jkrame1/Betweener/Hardware/panel/Kyle Werle Betweener and sidecar.jpg

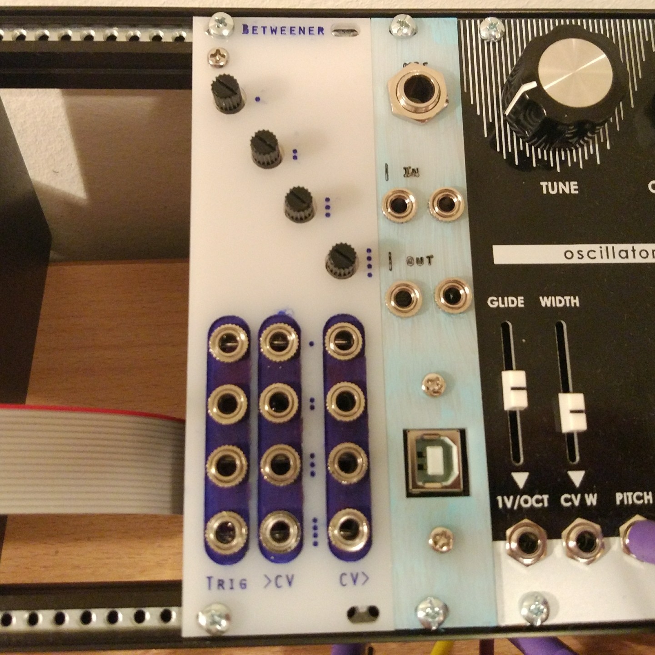
Hardware/panel/Kyle Werle Betweener and sidecar.jpg
