jkrame1/Betweener/Hardware/Betweener Build Images/Betweener-01.jpg

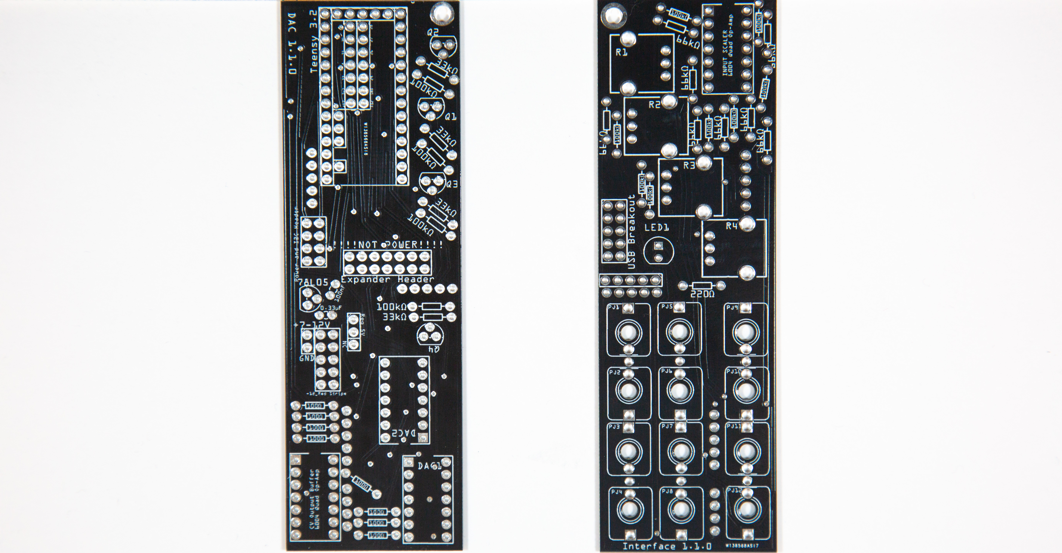
Hardware/Betweener Build Images/Betweener-01.jpg
