jkrame1/Betweener/Hardware/Betweener Build Images/Betweener-02.jpg

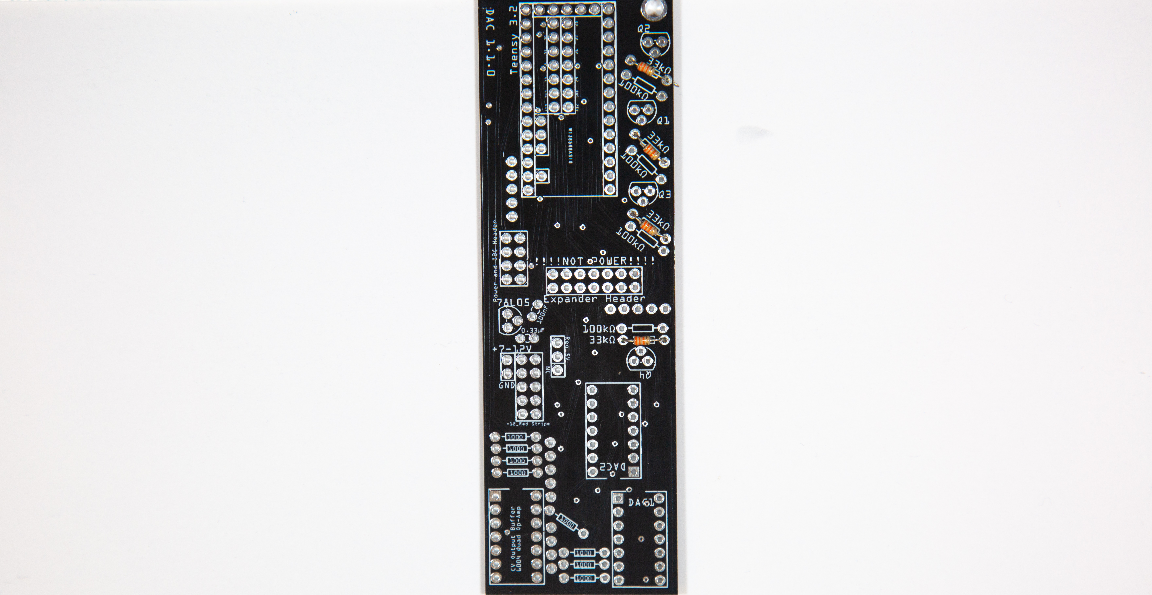
Hardware/Betweener Build Images/Betweener-02.jpg
