jkrame1/Betweener/Hardware/Betweener Build Images/Betweener-29.jpg

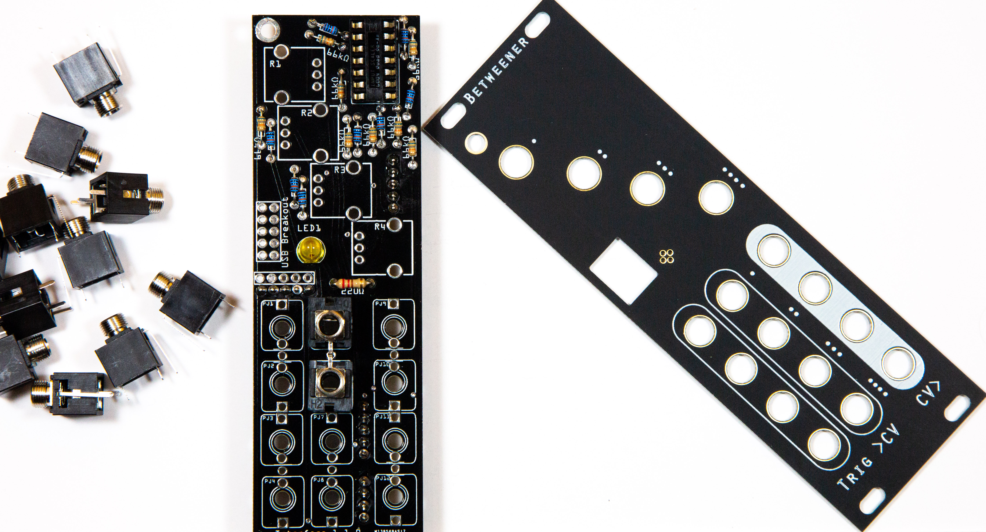
Hardware/Betweener Build Images/Betweener-29.jpg
