jkrame1/Betweener/Hardware/Betweener Build Images/Betweener-30.jpg

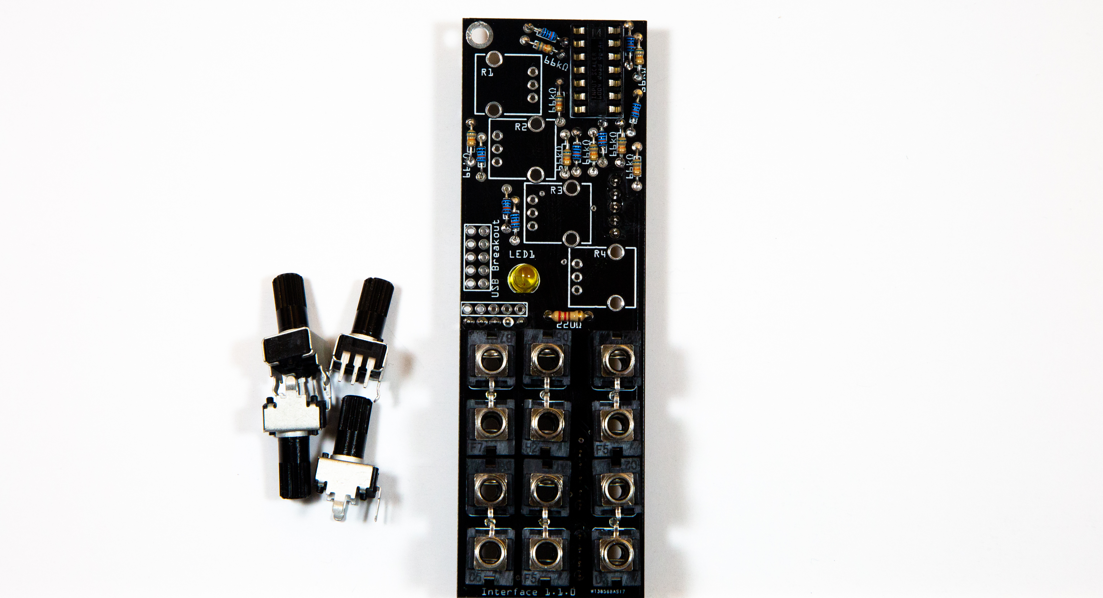
Hardware/Betweener Build Images/Betweener-30.jpg
