jkrame1/Betweener/Hardware/Betweener Build Images/Betweener-31.jpg

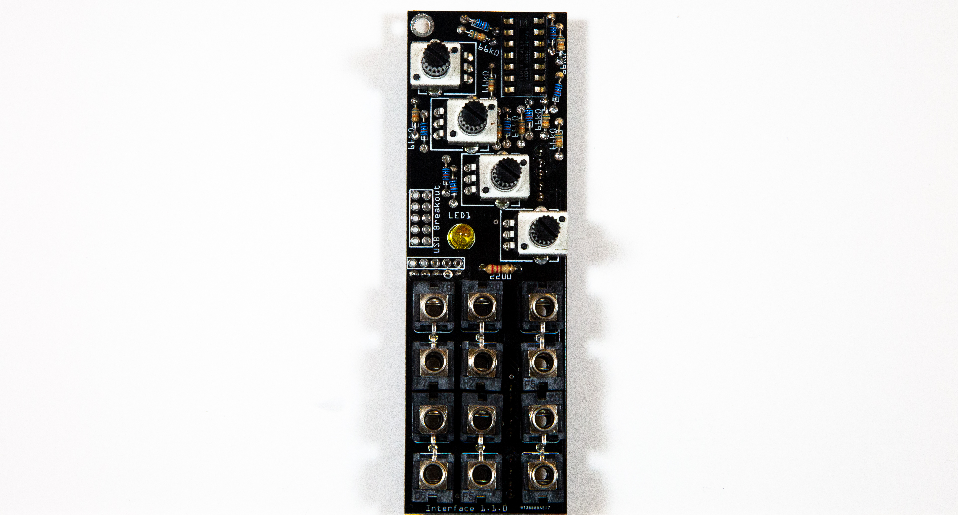
Hardware/Betweener Build Images/Betweener-31.jpg
