jkrame1/Betweener/Hardware/Betweener Build Images/Betweener-33.jpg

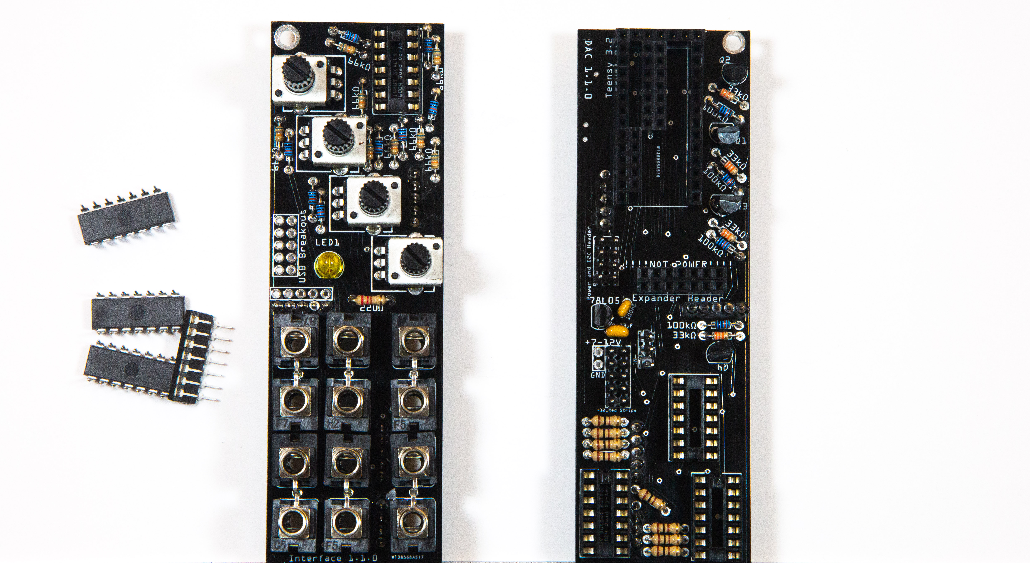
Hardware/Betweener Build Images/Betweener-33.jpg
