jkrame1/Betweener/Hardware/Betweener Build Images/Betweener-36.jpg

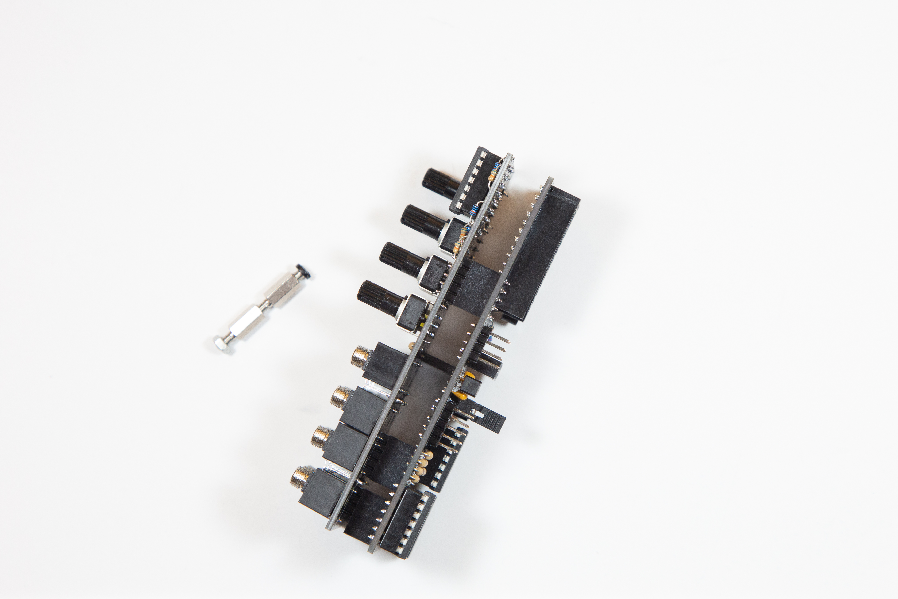
Hardware/Betweener Build Images/Betweener-36.jpg
