jkrame1/Betweener/Hardware/Betweener Build Images/Betweener-37.jpg

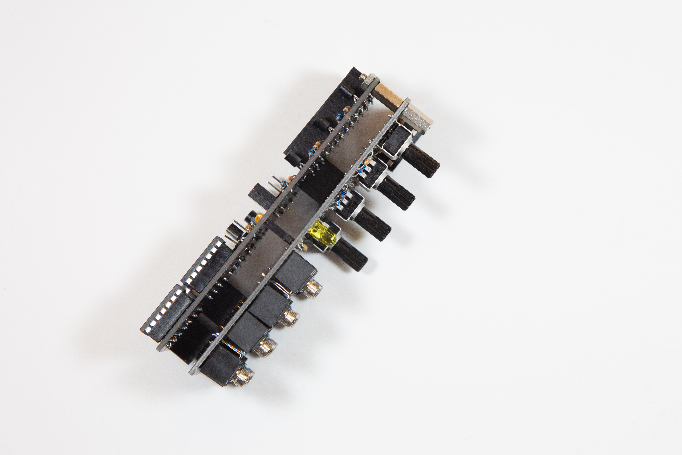
Hardware/Betweener Build Images/Betweener-37.jpg
