jkrame1/Betweener/Hardware/Betweener Build Images/Betweener-38.jpg

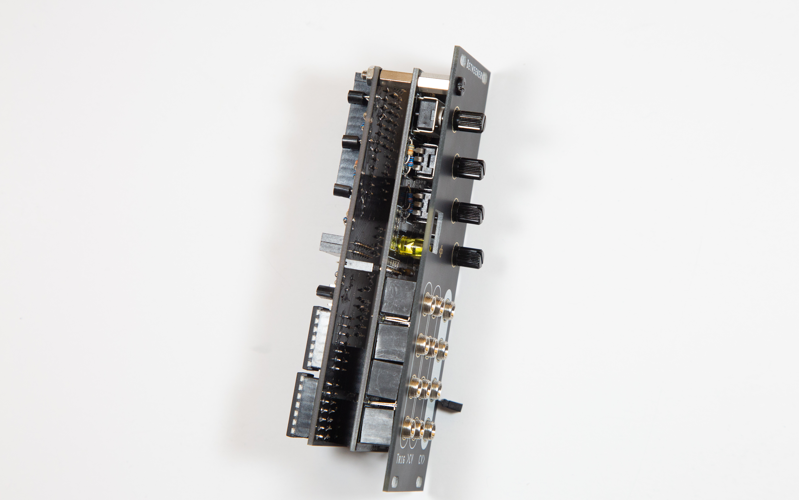
Hardware/Betweener Build Images/Betweener-38.jpg
