jkrame1/Betweener/Hardware/Betweener Build Images/Betweener-39.jpg

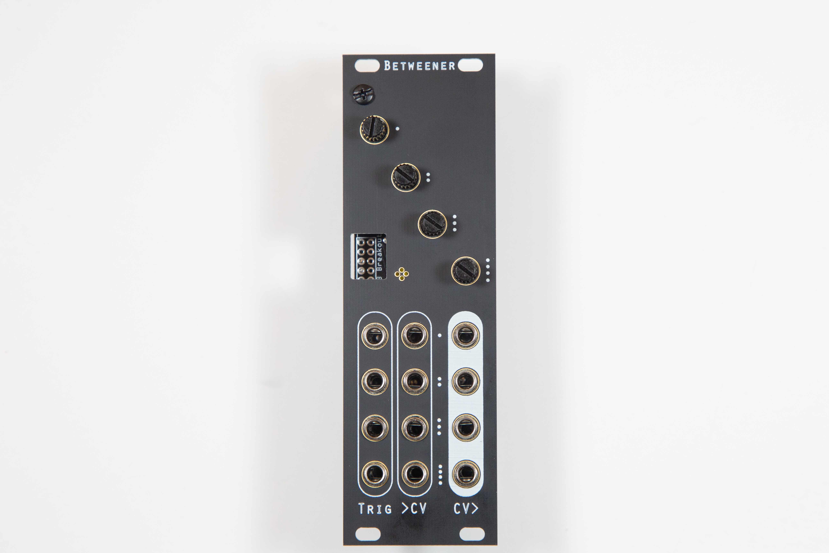
Hardware/Betweener Build Images/Betweener-39.jpg
