jkrame1/Betweener/Hardware/Betweener Build Images/Betweener-40.jpg

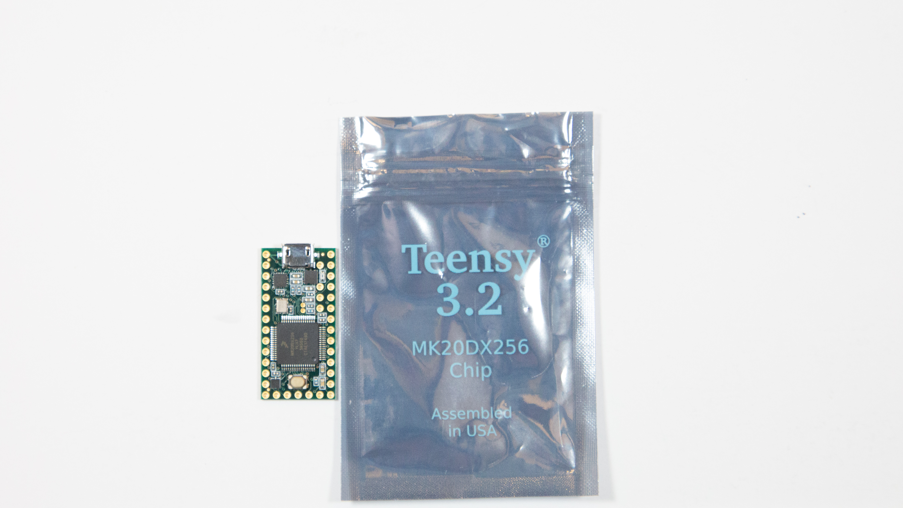
Hardware/Betweener Build Images/Betweener-40.jpg
