jkrame1/Betweener/Hardware/Betweener Build Images/Betweener-41.jpg

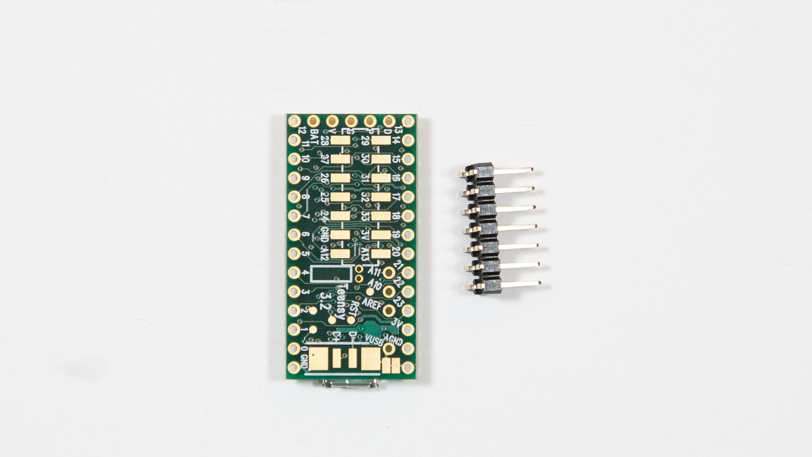
Hardware/Betweener Build Images/Betweener-41.jpg
