jkrame1/Betweener/Hardware/Betweener Build Images/Betweener-42.jpg

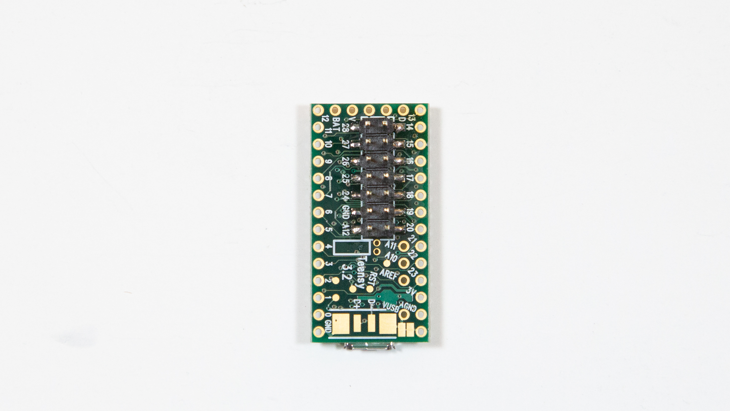
Hardware/Betweener Build Images/Betweener-42.jpg
