jkrame1/Betweener/Hardware/Betweener Build Images/Betweener-43.jpg

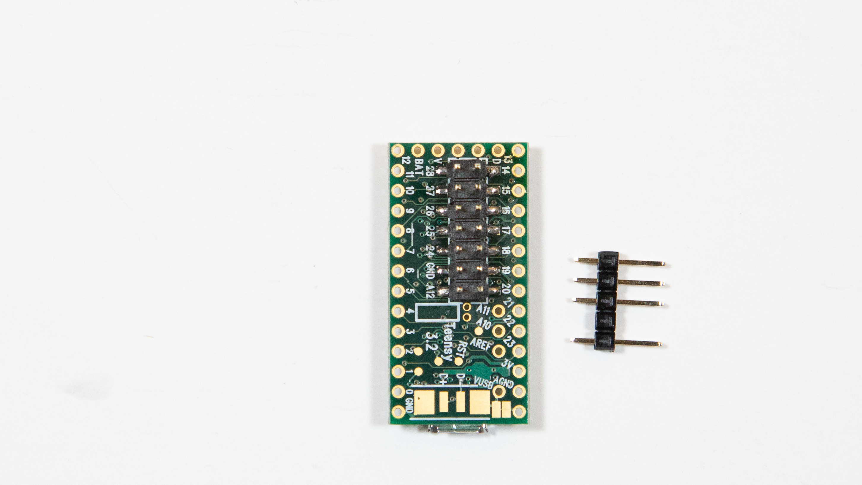
Hardware/Betweener Build Images/Betweener-43.jpg
