jkrame1/Betweener/Hardware/Betweener Build Images/Betweener-45.jpg

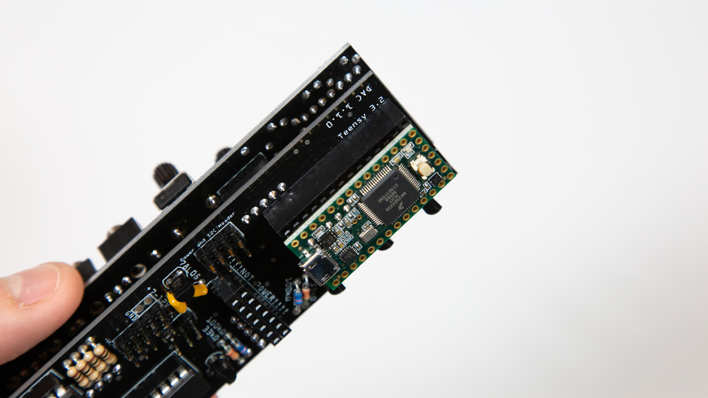
Hardware/Betweener Build Images/Betweener-45.jpg
