jkrame1/Betweener/Hardware/Betweener Build Images/Betweener-46.jpg

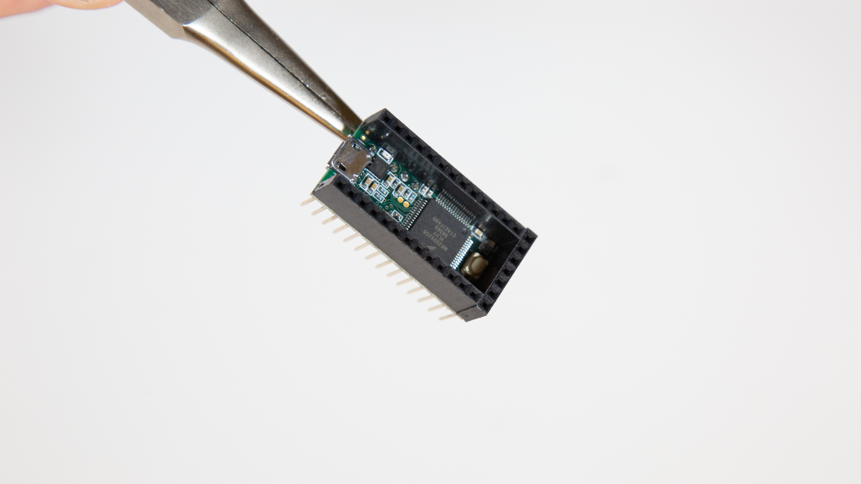
Hardware/Betweener Build Images/Betweener-46.jpg
