jkrame1/Betweener/Hardware/Betweener Build Images/Betweener-47.jpg

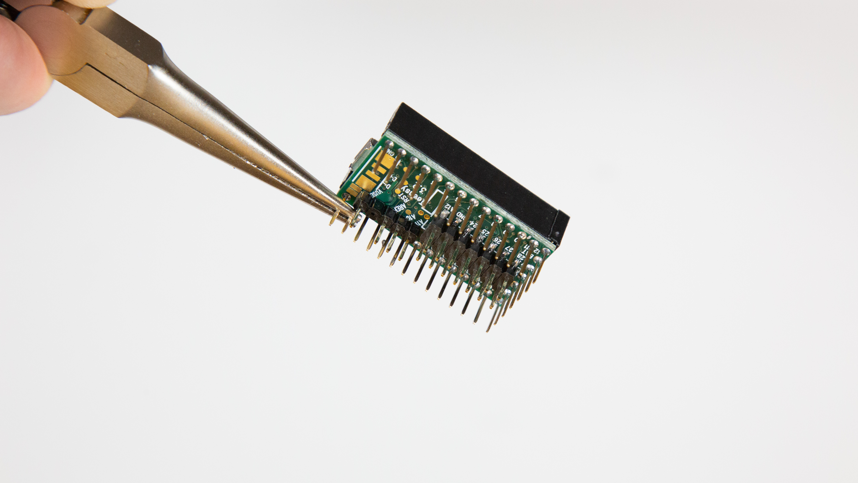
Hardware/Betweener Build Images/Betweener-47.jpg
