jkrame1/Betweener/Hardware/Betweener Build Images/Betweener-48.jpg

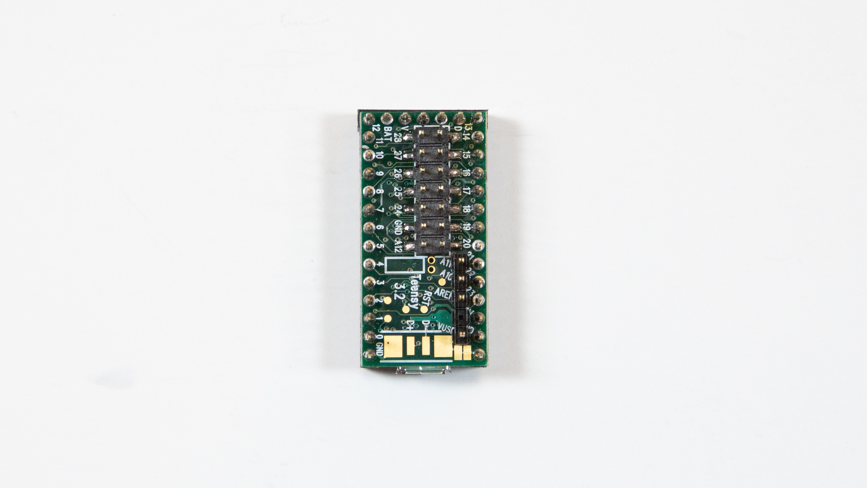
Hardware/Betweener Build Images/Betweener-48.jpg
