jkrame1/Betweener/Hardware/Betweener Build Images/Betweener-49.jpg

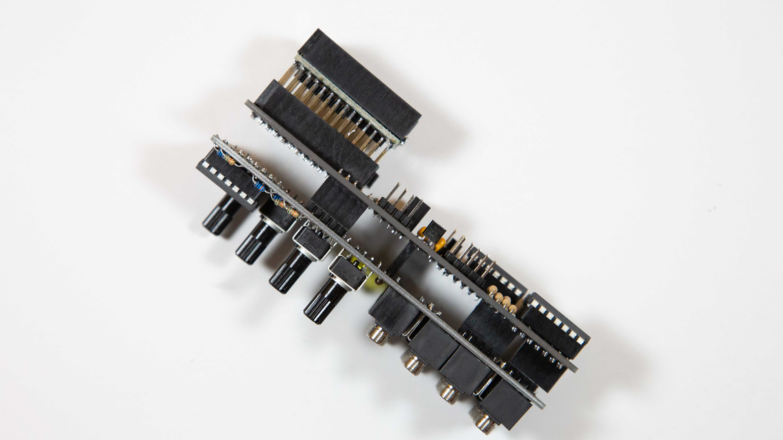
Hardware/Betweener Build Images/Betweener-49.jpg
