jkrame1/Betweener/Hardware/Betweener Build Images/Betweener-50.jpg

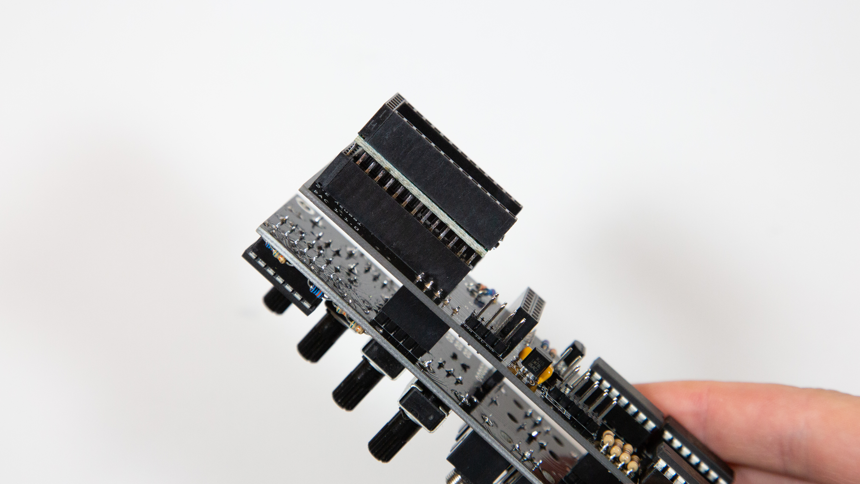
Hardware/Betweener Build Images/Betweener-50.jpg
