jkrame1/Betweener/Hardware/Betweener Build Images/Betweener-51.jpg

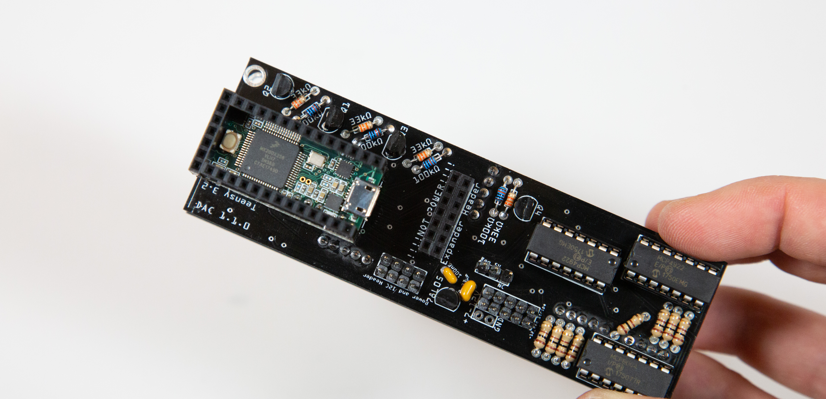
Hardware/Betweener Build Images/Betweener-51.jpg
