jkrame1/Betweener/Hardware/Betweener Build Images/Betweener-54.jpg

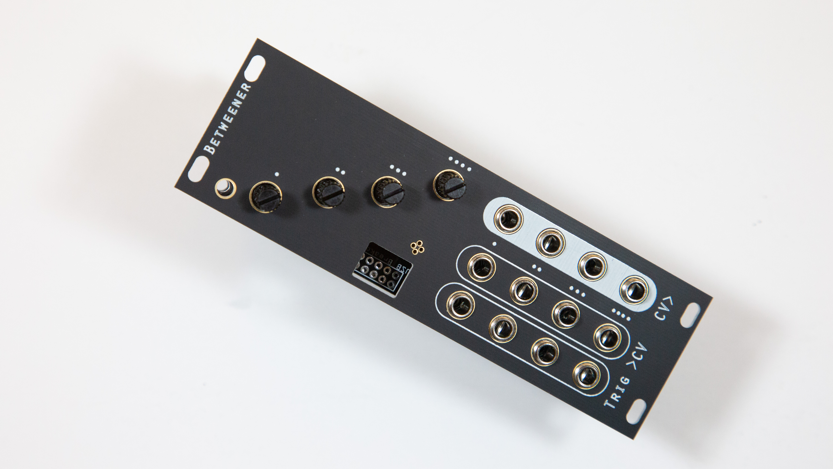
Hardware/Betweener Build Images/Betweener-54.jpg
