jkrame1/Betweener/Hardware/Betweener Build Images/Betweener-55.jpg

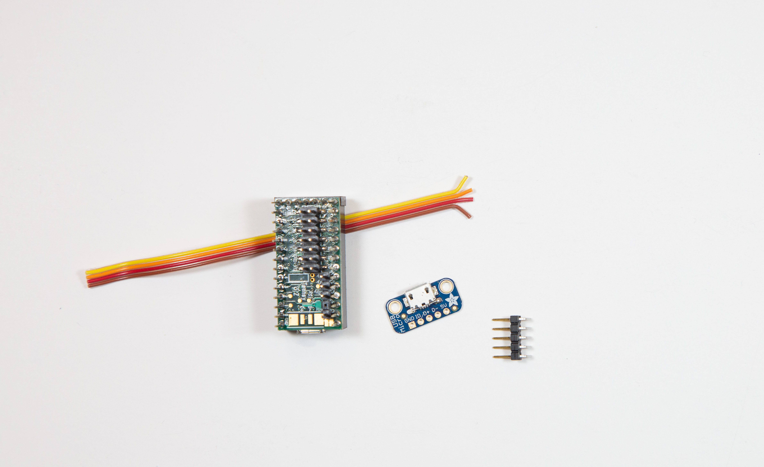
Hardware/Betweener Build Images/Betweener-55.jpg
