jkrame1/Betweener/Hardware/Betweener Build Images/Betweener-56.jpg

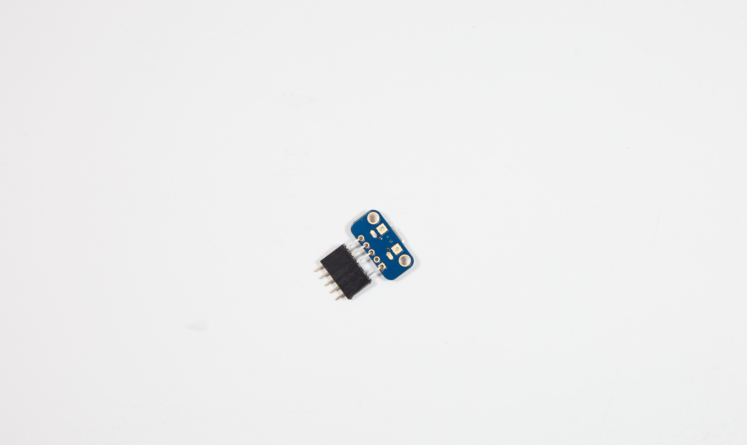
Hardware/Betweener Build Images/Betweener-56.jpg
