jkrame1/Betweener/Hardware/Betweener Build Images/Betweener-57.jpg

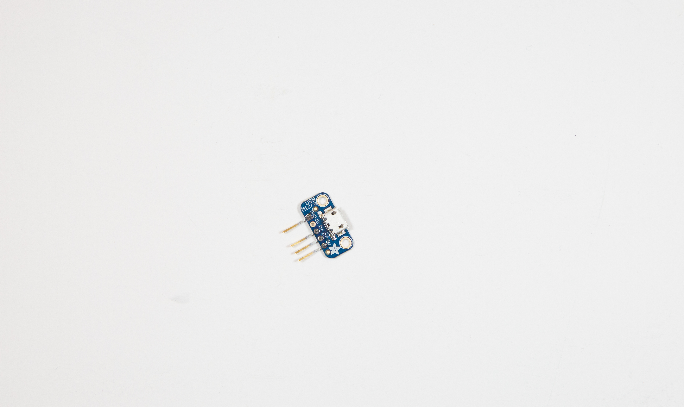
Hardware/Betweener Build Images/Betweener-57.jpg
