jkrame1/Betweener/Hardware/Betweener Build Images/Betweener-58.jpg

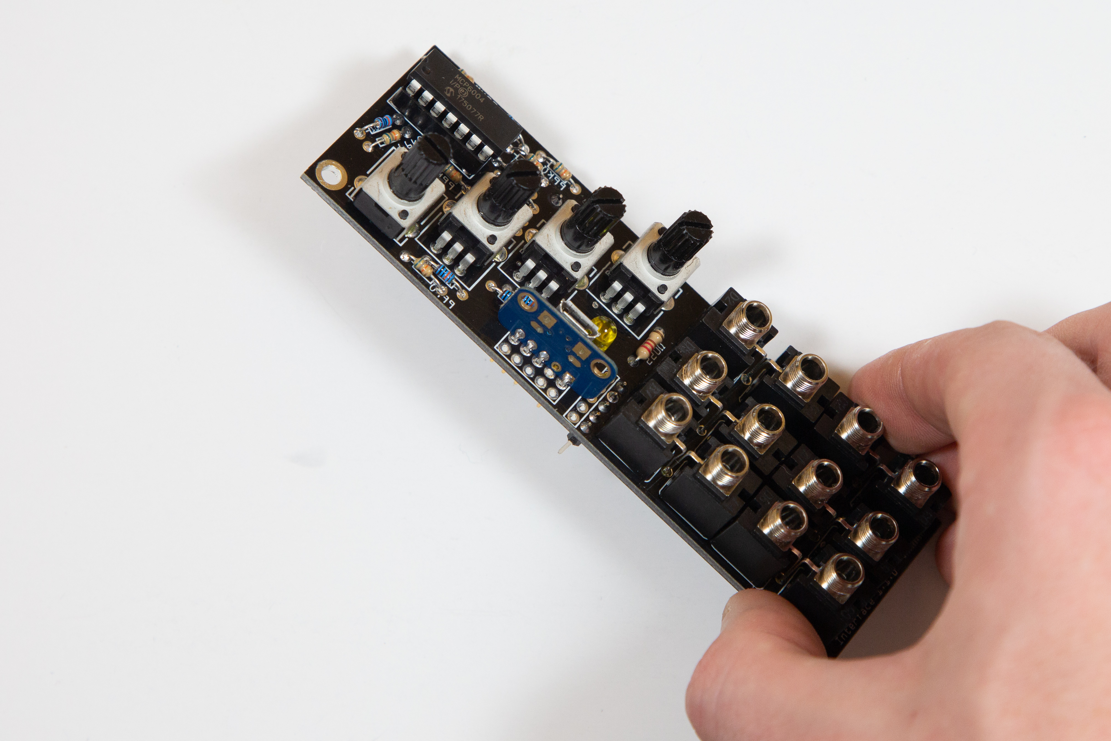
Hardware/Betweener Build Images/Betweener-58.jpg
