jkrame1/Betweener/Hardware/Betweener Build Images/Betweener-59.jpg

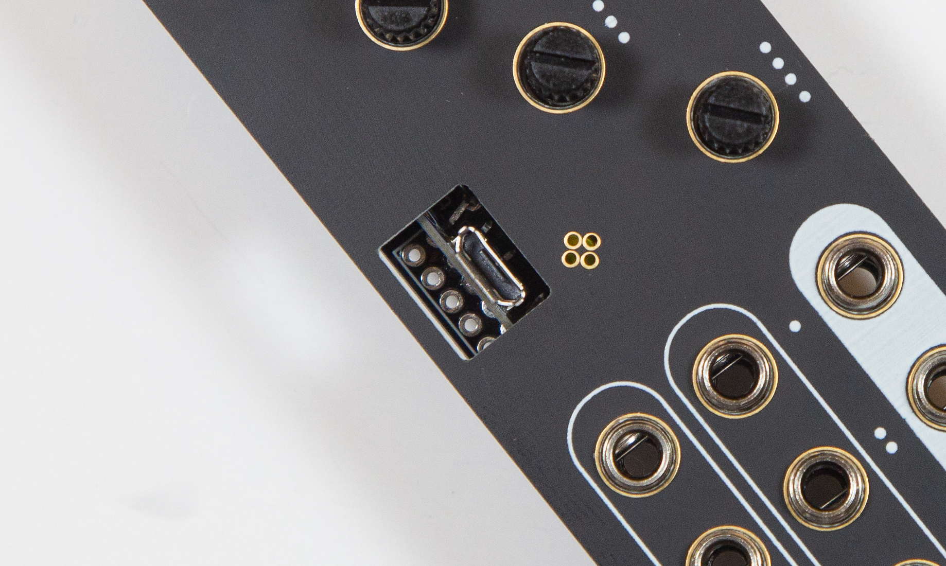
Hardware/Betweener Build Images/Betweener-59.jpg
