jkrame1/Betweener/Hardware/Betweener Build Images/Betweener-60.jpg

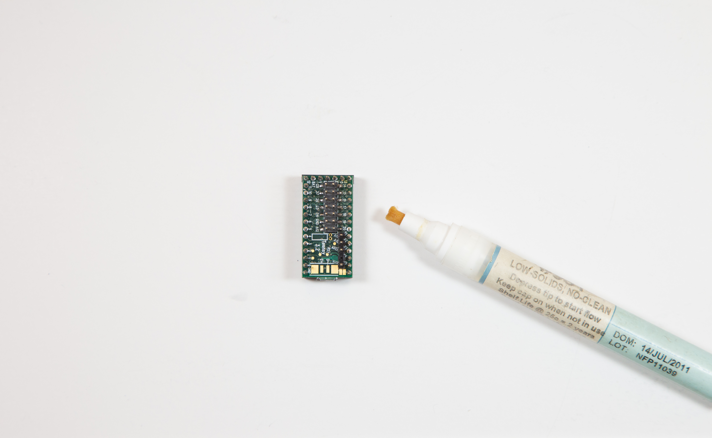
Hardware/Betweener Build Images/Betweener-60.jpg
