jkrame1/Betweener/Hardware/Betweener Build Images/Betweener-61.jpg

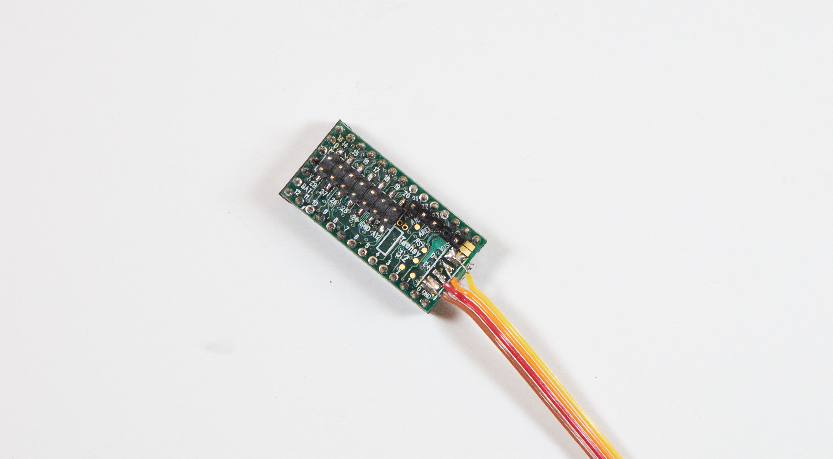
Hardware/Betweener Build Images/Betweener-61.jpg
