jkrame1/Betweener/Hardware/Betweener Build Images/Betweener-62.jpg

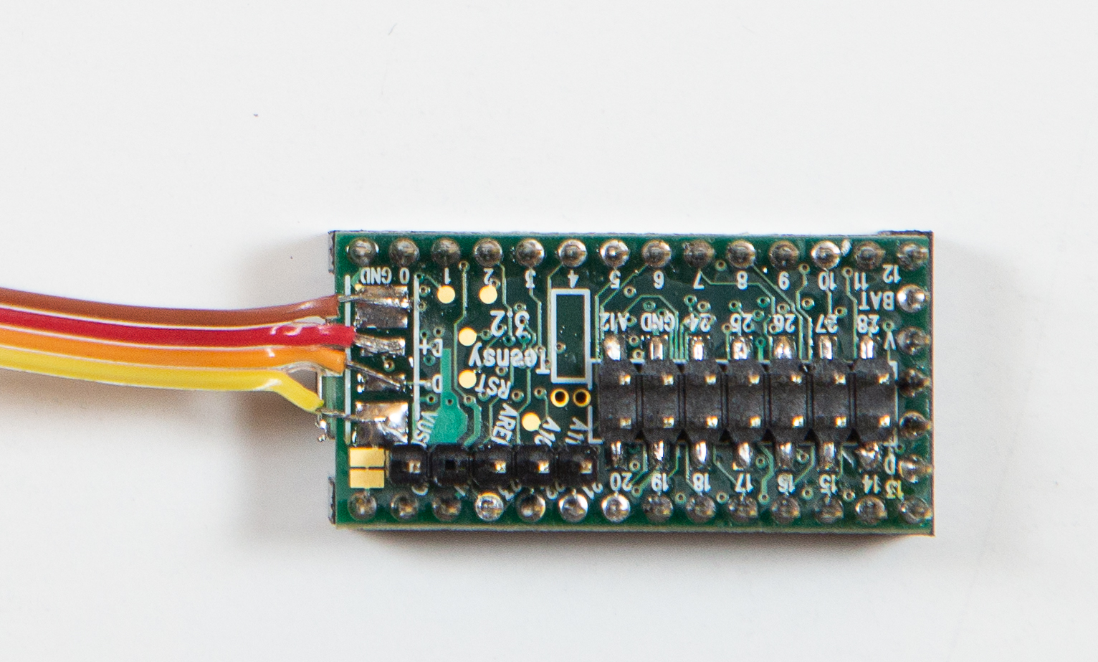
Hardware/Betweener Build Images/Betweener-62.jpg
