jkrame1/Betweener/Hardware/Betweener Build Images/Betweener-63.jpg

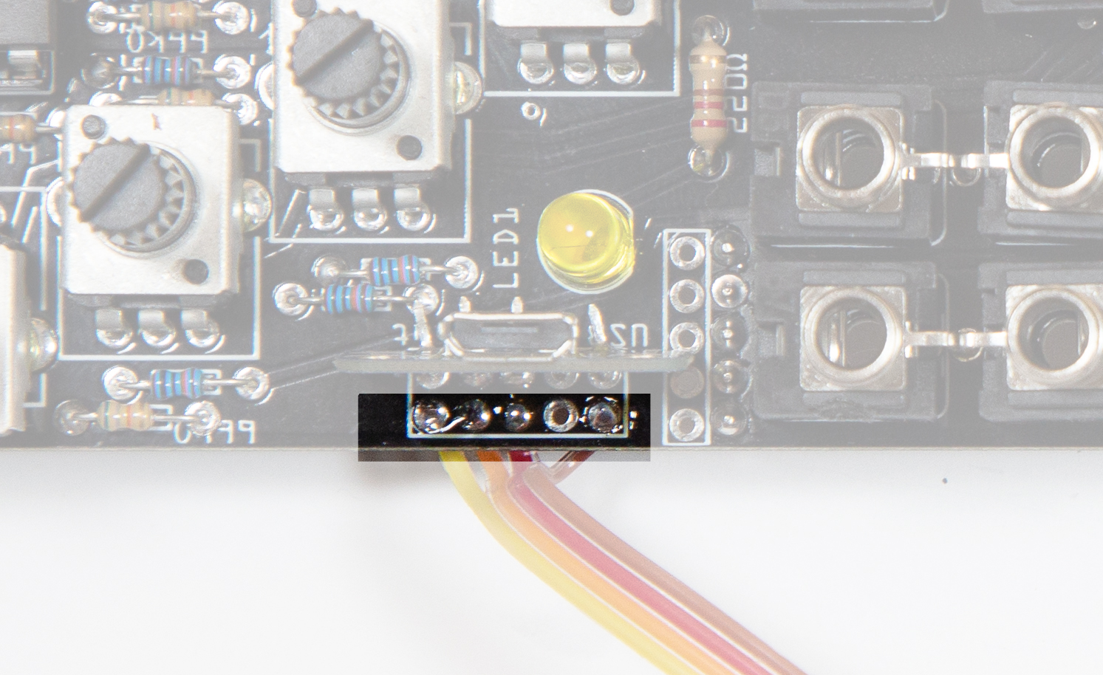
Hardware/Betweener Build Images/Betweener-63.jpg
