jkrame1/Betweener/Hardware/Betweener Build Images/Betweener-64.jpg

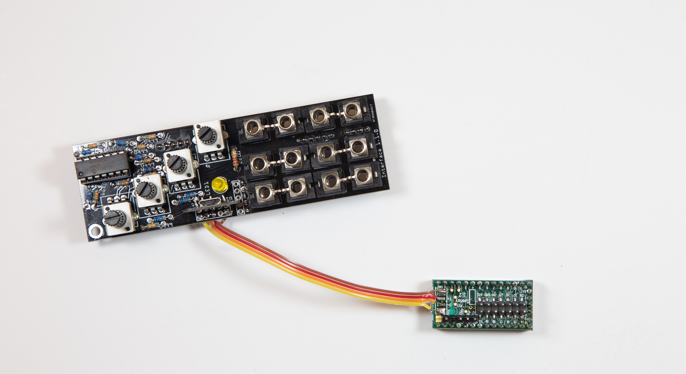
Hardware/Betweener Build Images/Betweener-64.jpg
