jkrame1/Betweener/Hardware/Betweener Build Images/Betweener-65_EurorackPowerOnly.jpg

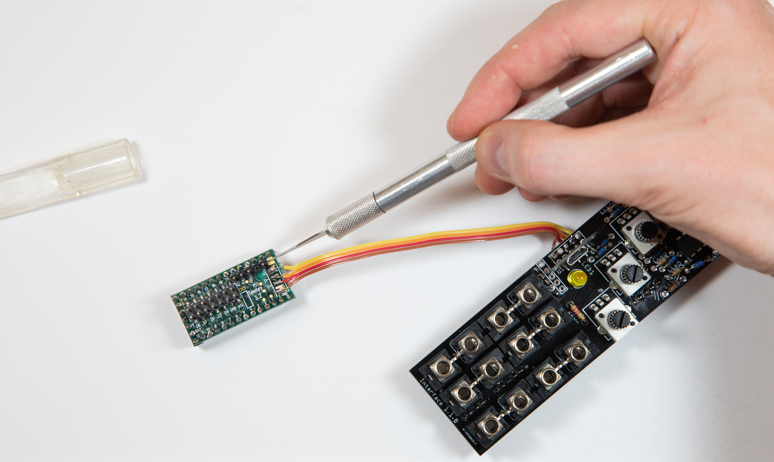
Hardware/Betweener Build Images/Betweener-65_EurorackPowerOnly.jpg
