jkrame1/Betweener/Hardware/Betweener Build Images/Betweener-66_EurorackPowerOnly.jpg

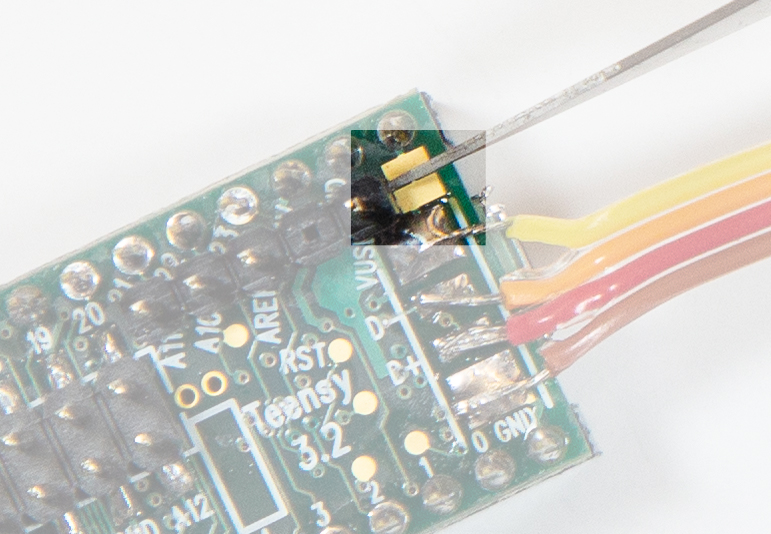
Hardware/Betweener Build Images/Betweener-66_EurorackPowerOnly.jpg
