jkrame1/Betweener/Hardware/Betweener Build Images/Betweener-67.jpg

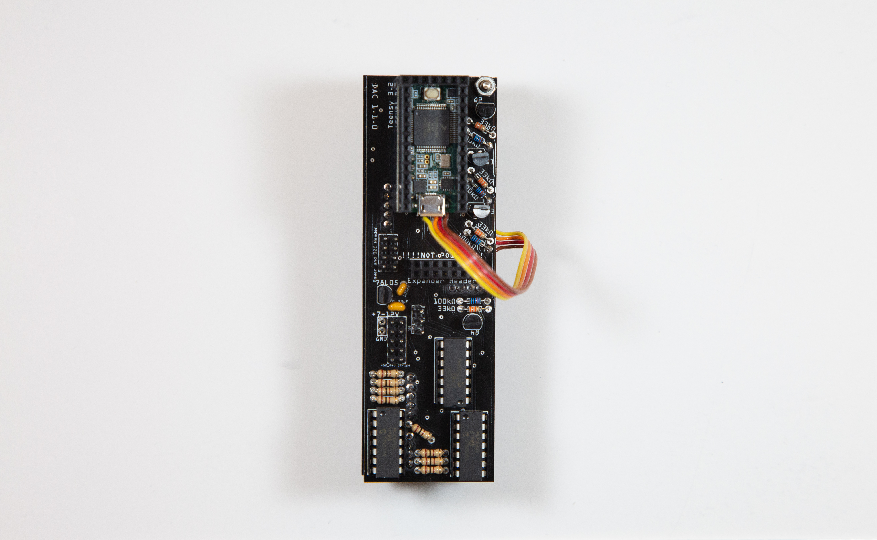
Hardware/Betweener Build Images/Betweener-67.jpg
