jkrame1/Betweener/Hardware/Betweener Build Images/Betweener-68.jpg

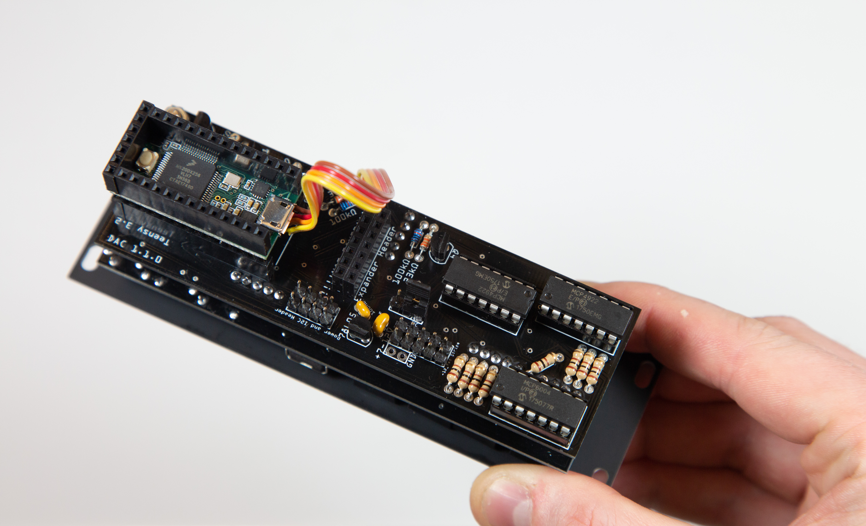
Hardware/Betweener Build Images/Betweener-68.jpg
