jkrame1/Betweener/Hardware/Betweener Build Images/Betweener-69.jpg

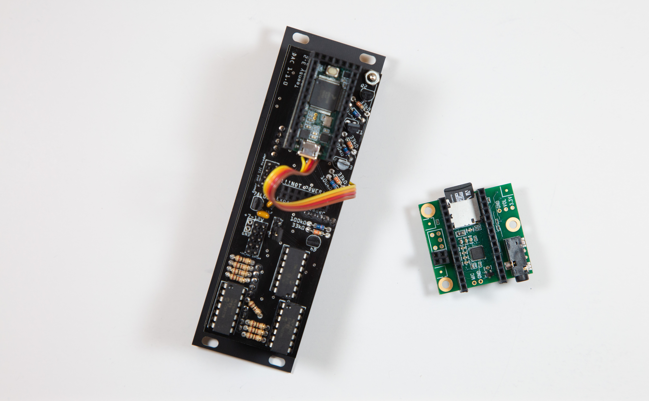
Hardware/Betweener Build Images/Betweener-69.jpg
