jkrame1/Betweener/Hardware/Betweener Build Images/Betweener-70.jpg

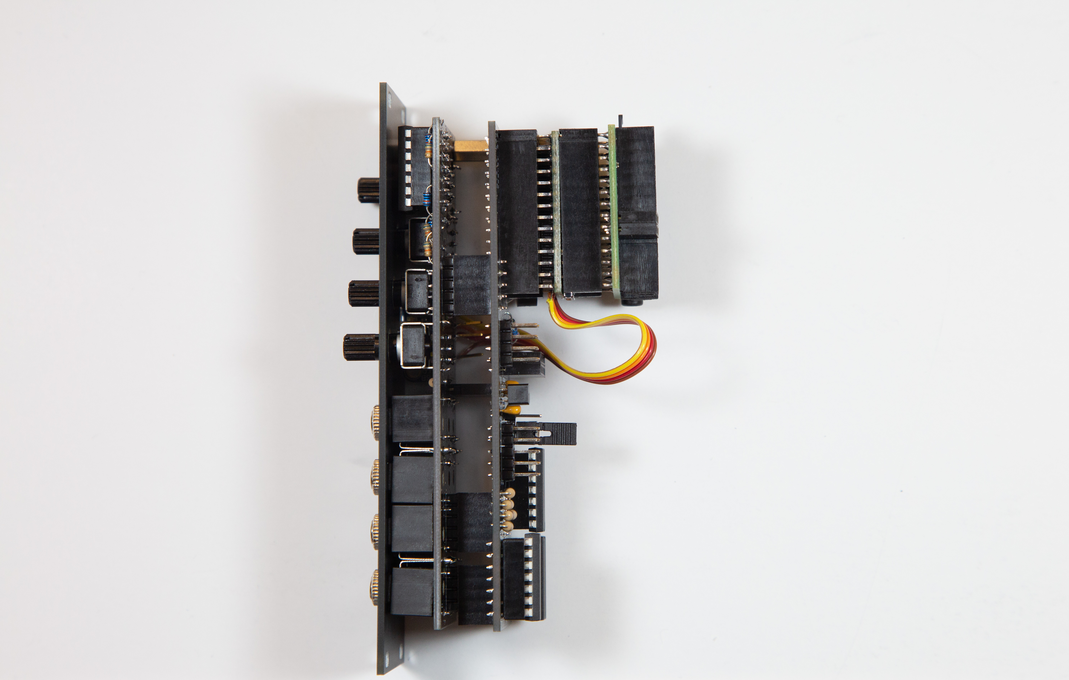
Hardware/Betweener Build Images/Betweener-70.jpg
