jkrame1/Betweener/Hardware/Betweener Build Images/Betweener-71_CutTraceONLY.jpg

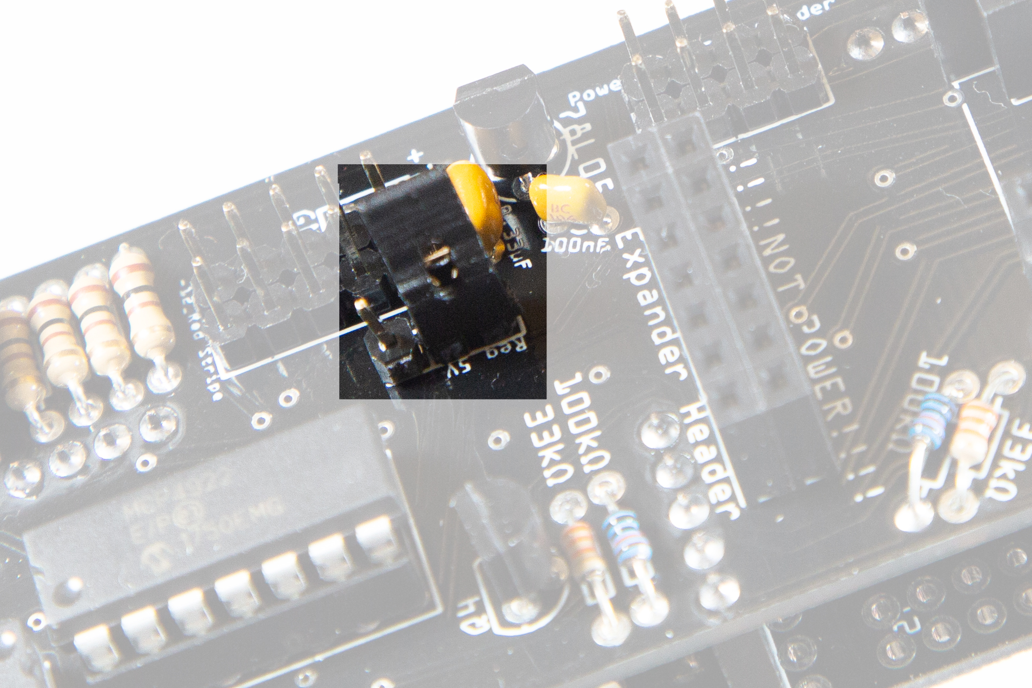
Hardware/Betweener Build Images/Betweener-71_CutTraceONLY.jpg
