jkrame1/Betweener/Hardware/Betweener Build Images/Betweener-72_USBPower.jpg

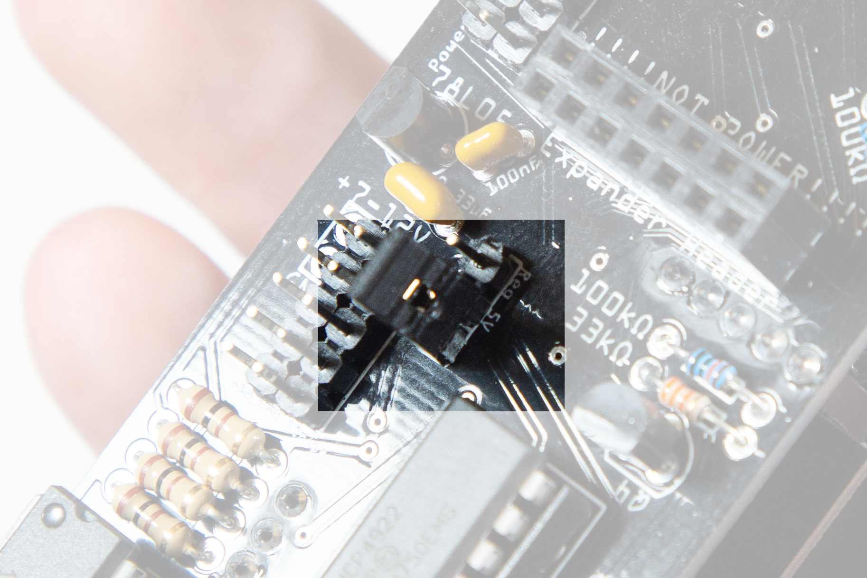
Hardware/Betweener Build Images/Betweener-72_USBPower.jpg
