jkrame1/Betweener/Hardware/Betweener Build Images/Betweener-73.jpg

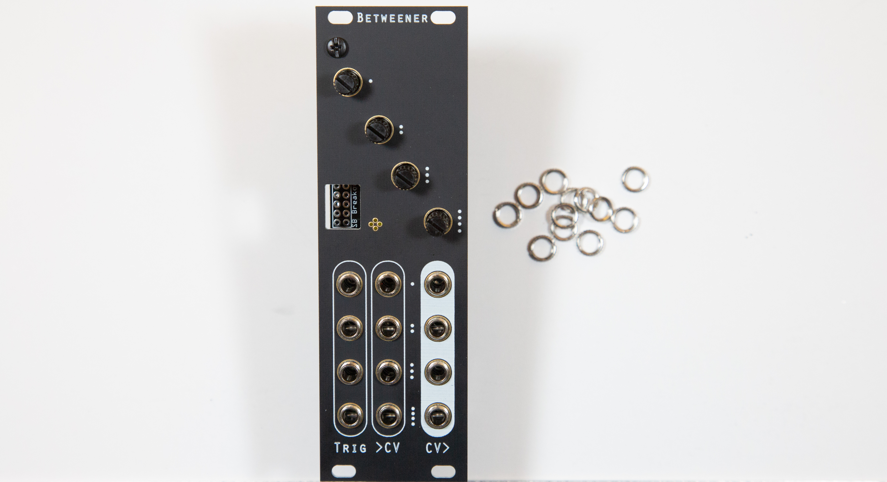
Hardware/Betweener Build Images/Betweener-73.jpg
