jkrame1/Betweener/Hardware/Betweener Build Images/Betweener-74.jpg

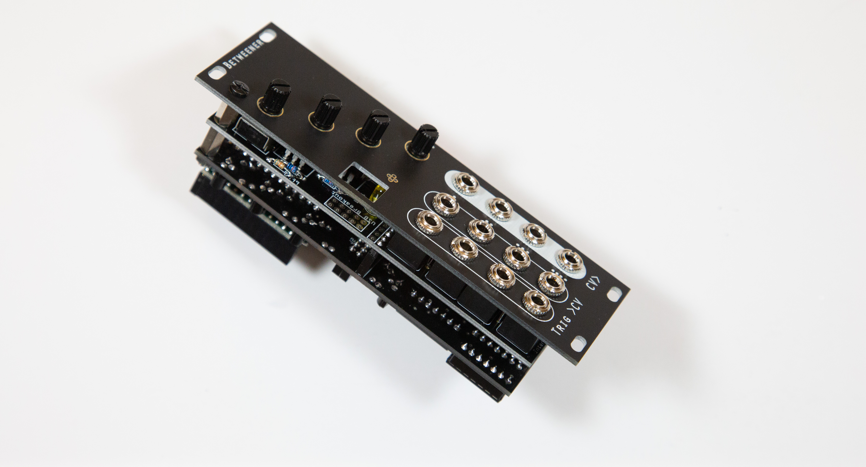
Hardware/Betweener Build Images/Betweener-74.jpg
